jkordek1/Man-Don-t-Get-Angry-Board-game/Images/back.jpg

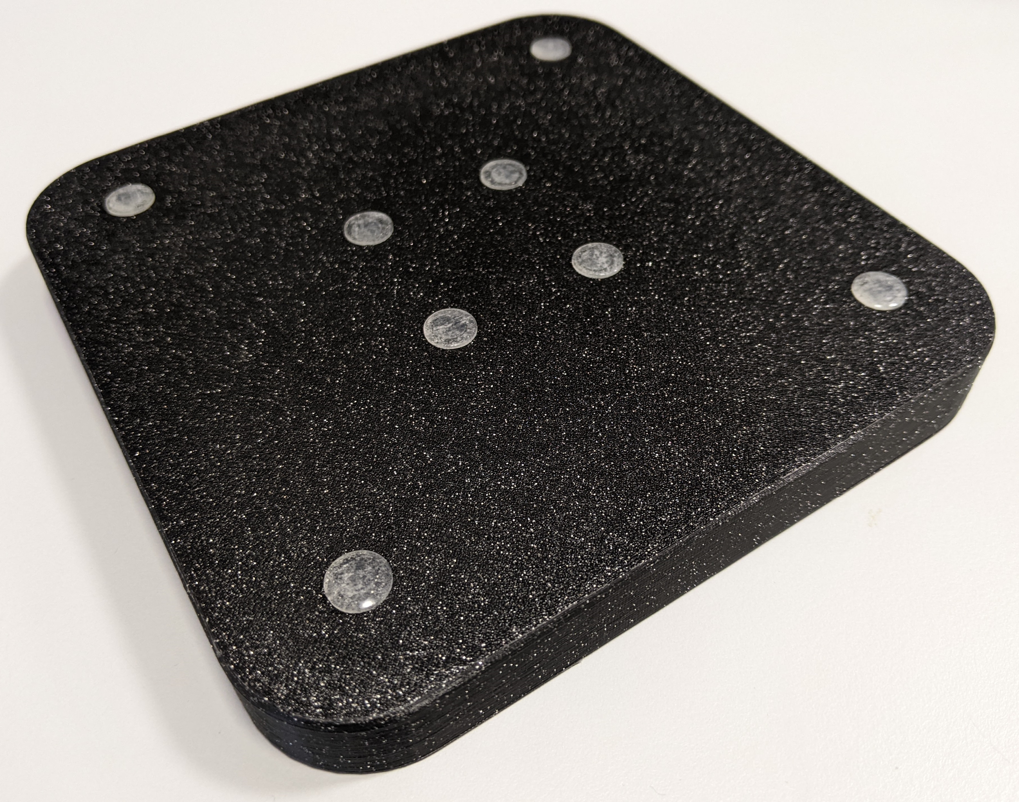
Images/back.jpg
