jkordek1/Man-Don-t-Get-Angry-Board-game/Images/front1.jpg

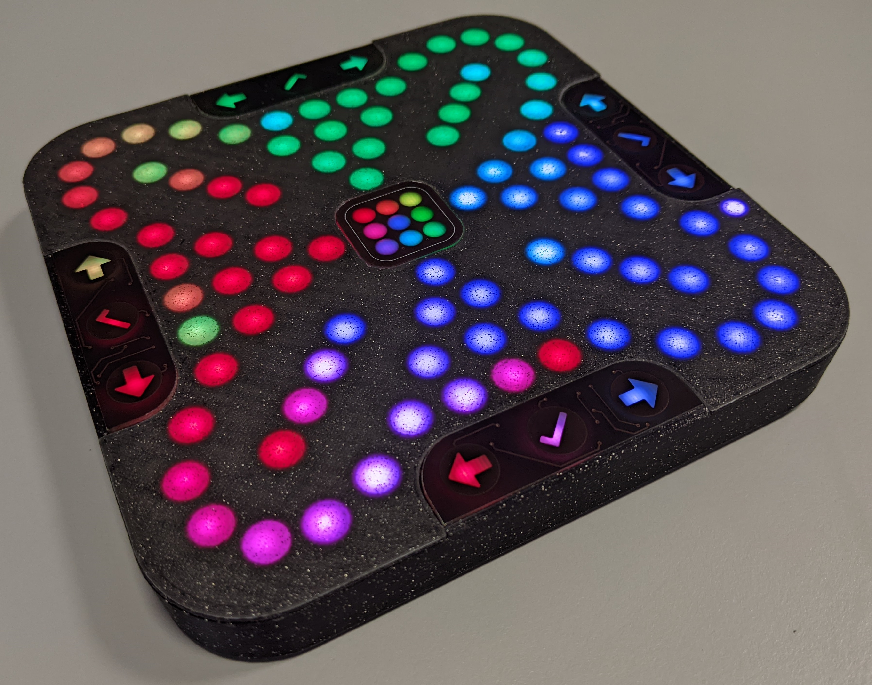
Images/front1.jpg
