jkordek1/Man-Don-t-Get-Angry-Board-game/Images/front2.jpg

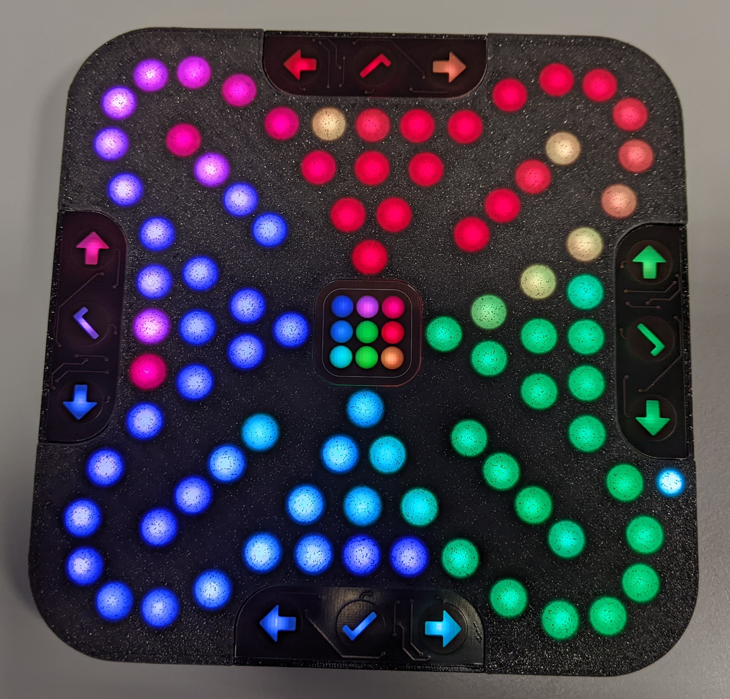
Images/front2.jpg
