jkordek1/Man-Don-t-Get-Angry-Board-game/Images/Positions.png

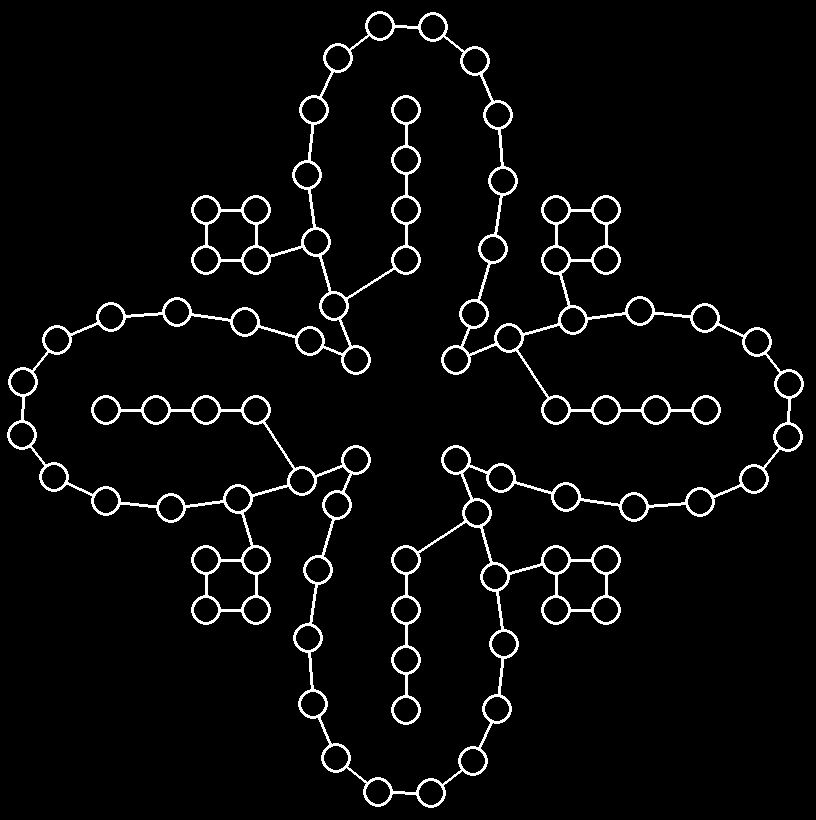
Images/Positions.png
