jkordek1/Man-Don-t-Get-Angry-Board-game/Images/Positions_v2.png

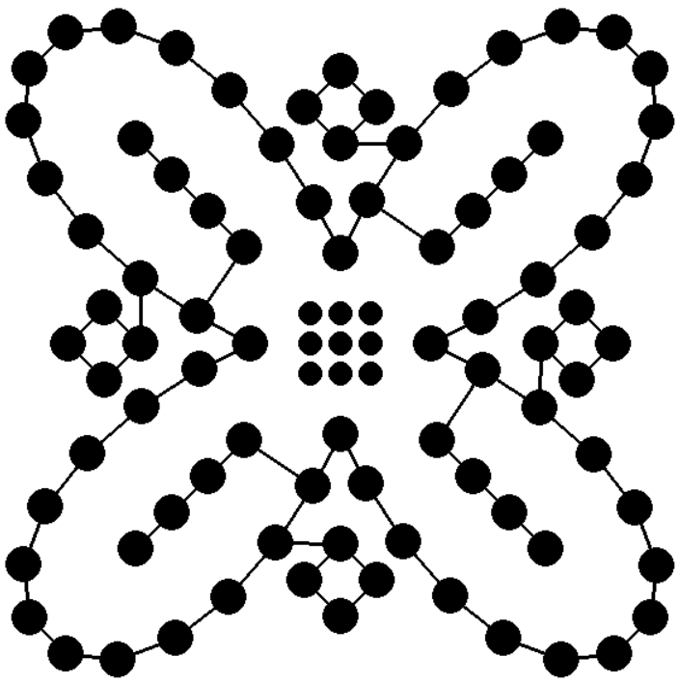
Images/Positions_v2.png
