jkordek1/Man-Don-t-Get-Angry-Board-game/Solidworks assembly/Case_v2.SLDPRT

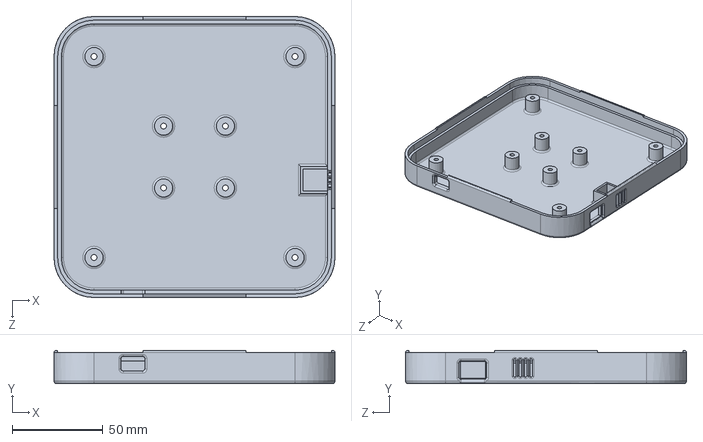
[picture p31: CAD file, 2022-11-10]
Solidworks assembly/Case_v2.SLDPRT
154.5 x 18.4 x 154.5 mm
