jkordek1/Man-Don-t-Get-Angry-Board-game/KiCad files/3D models/WS2812B.step

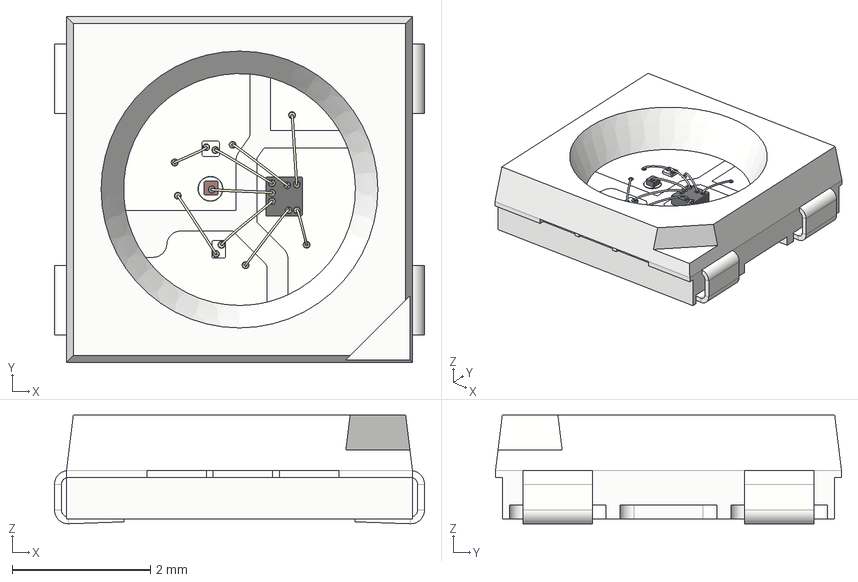
[picture p32: CAD file, 2022-06-08]
KiCad files/3D models/WS2812B.step
5.35 x 5.00 x 1.57 mm
