jkordek1/Man-Don-t-Get-Angry-Board-game/KiCad files/3D models/WS2812B Mini.step

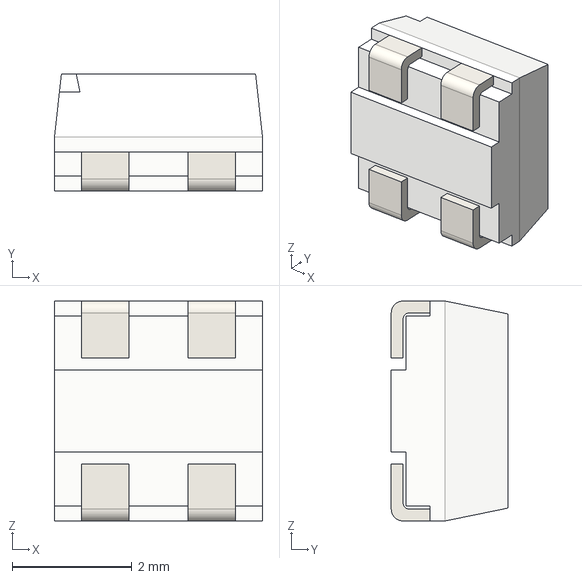
[picture p33: CAD file, 2022-04-26]
KiCad files/3D models/WS2812B Mini.step
3.48 x 1.95 x 3.68 mm
