jkordek1/Man-Don-t-Get-Angry-Board-game/KiCad files/3D models/WS2812-4020.STEP

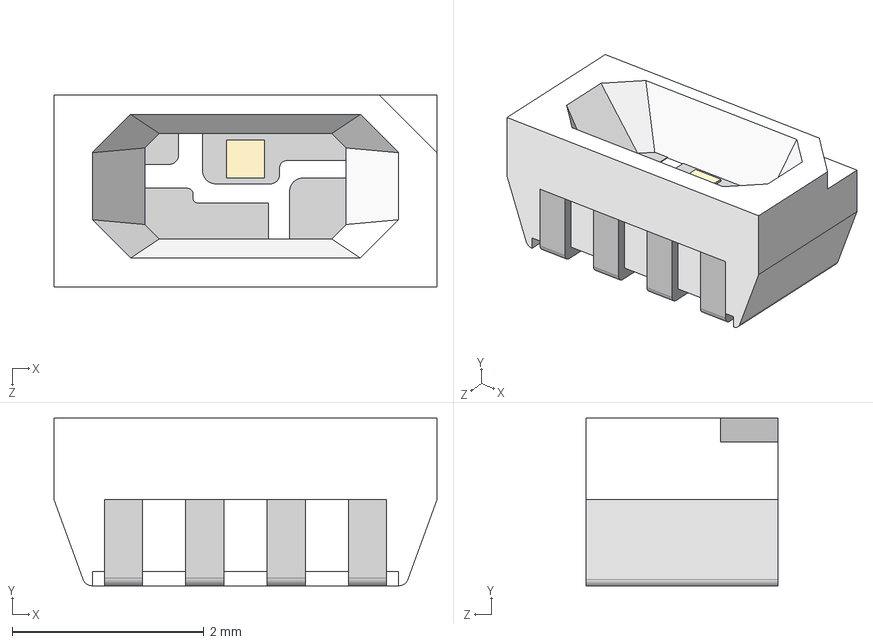
[picture p34: CAD file, 2022-04-19]
KiCad files/3D models/WS2812-4020.STEP
4.00 x 1.75 x 2.00 mm
