jkordek1/Man-Don-t-Get-Angry-Board-game/Solidworks assembly/Tornillo plastico negro M3x6mm.SLDPRT

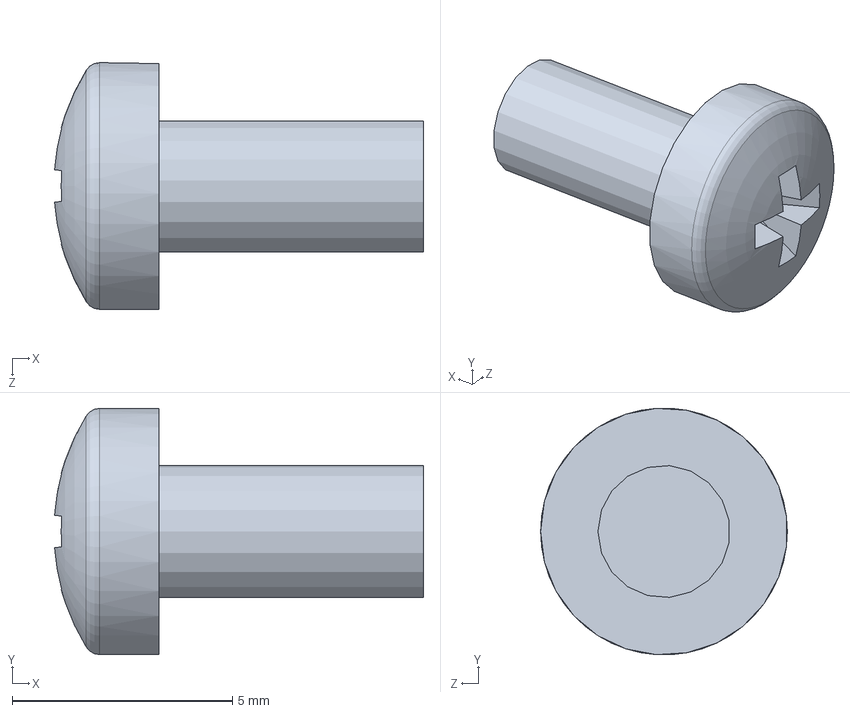
[picture p35: CAD file, 2022-11-07]
Solidworks assembly/Tornillo plastico negro M3x6mm.SLDPRT
8.37 x 5.59 x 5.60 mm
