jkordek1/Man-Don-t-Get-Angry-Board-game/Solidworks assembly/PRK22J5DBBNN.SLDPRT

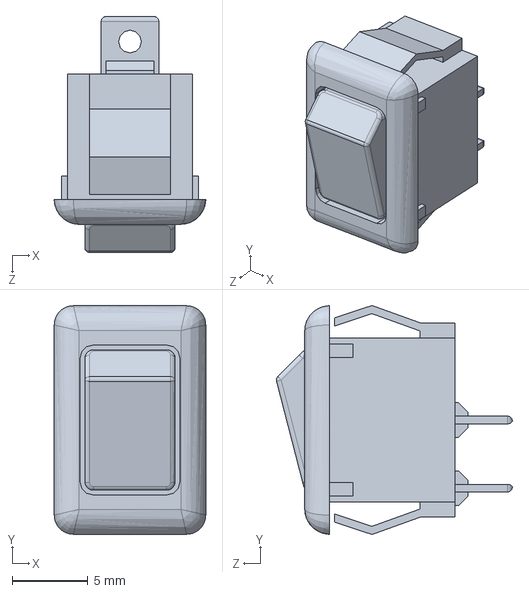
[picture p36: CAD file, 2022-11-04]
Solidworks assembly/PRK22J5DBBNN.SLDPRT
10.0 x 15.1 x 15.6 mm
