jkordek1/Man-Don-t-Get-Angry-Board-game/Images/LED2-test.PNG

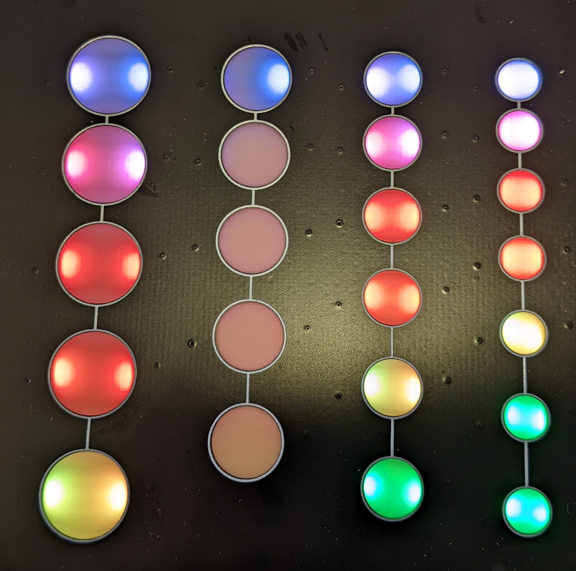
Images/LED2-test.PNG
