jkordek1/Man-Don-t-Get-Angry-Board-game/Images/LED-test.PNG

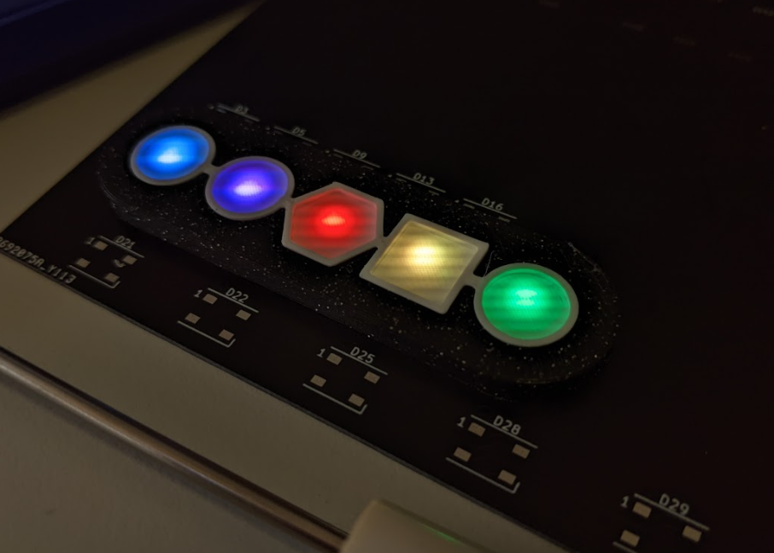
Images/LED-test.PNG
