jkordek1/Man-Don-t-Get-Angry-Board-game/Images/touchpad-test.PNG

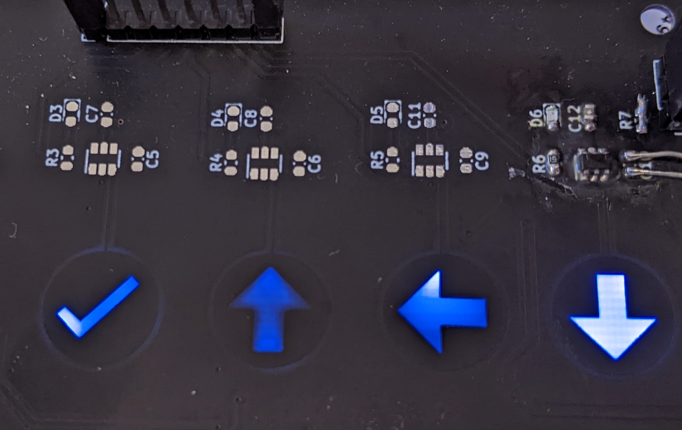
Images/touchpad-test.PNG
